anhldptit2610/dalws/hardware/dalws/dalws.kicad_sch

## KiCad design hardware/dalws/dalws.kicad_sch (2024-07-06)

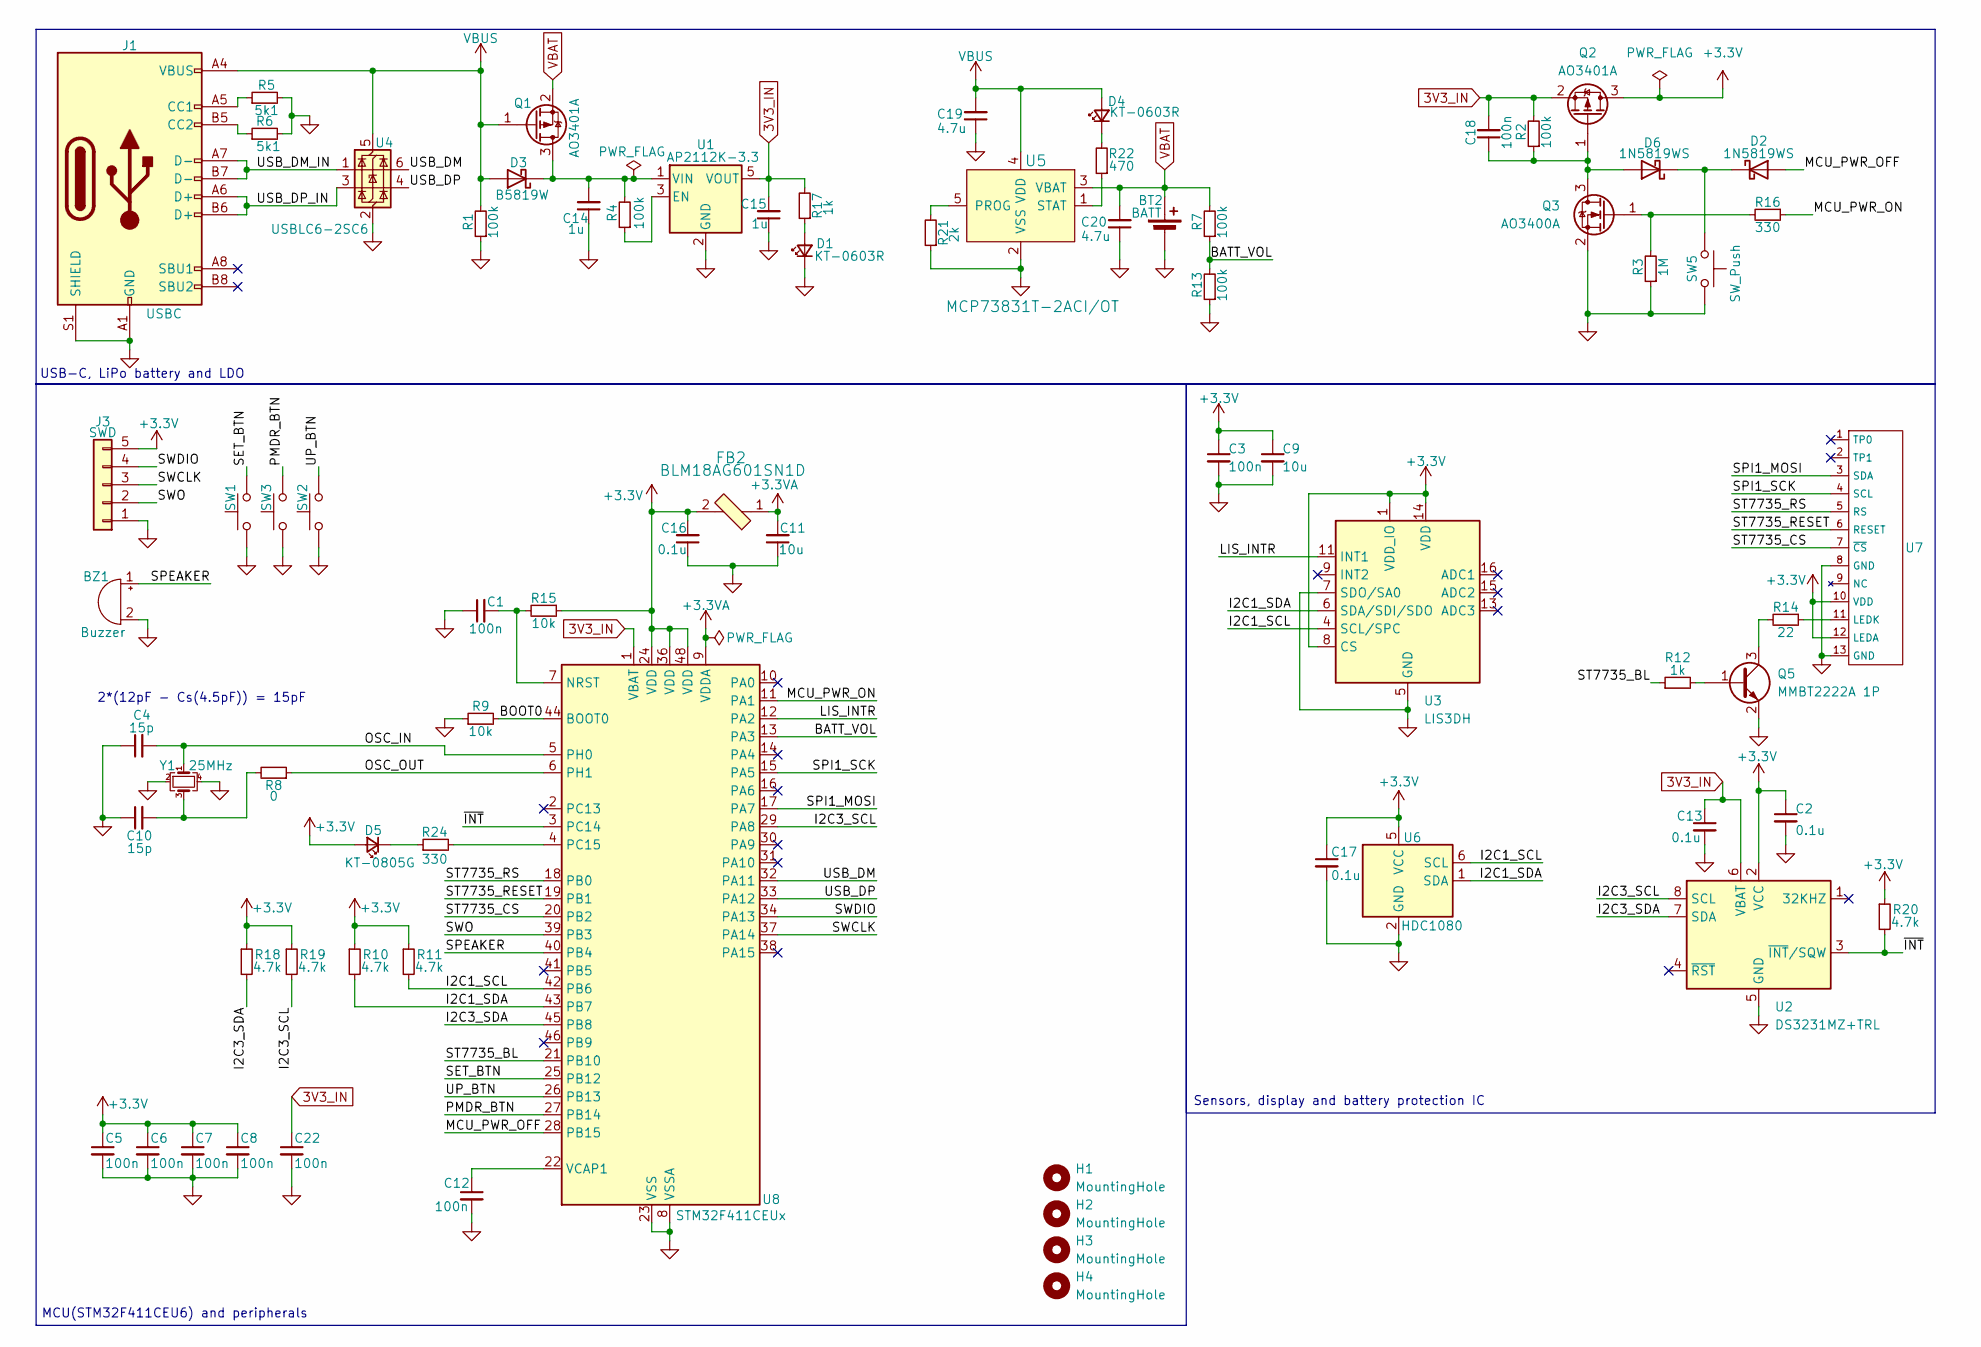
[picture p3: schematic dalws.kicad_sch]

Parts:
BT2: BATT; PinHeader_1x02_P2.54mm_Vertical
BZ1: Buzzer; TMB09A05
C1, C3, C5, C6, C7, C8, C12, C18, C22: 100n; C_0402_1005Metric_Pad0.74x0.62mm_HandSolder
C2, C13, C16, C17: 0.1u; C_0402_1005Metric_Pad0.74x0.62mm_HandSolder
C4, C10: 15p; C_0402_1005Metric_Pad0.74x0.62mm_HandSolder
C9, C11: 10u; C_0402_1005Metric_Pad0.74x0.62mm_HandSolder
C14, C15: 1u; C_0402_1005Metric_Pad0.74x0.62mm_HandSolder
C19, C20: 4.7u; C_0805_2012Metric
D1, D4: KT-0603R; LED_0603_1608Metric_Pad1.05x0.95mm_HandSolder
D2, D6: 1N5819WS; D_SOD-323
D3: B5819W
D5: KT-0805G; LED_0603_1608Metric_Pad1.05x0.95mm_HandSolder
FB2: BLM18AG601SN1D; 0603; MPN BLM18AG601SN1D; Digi-Key_PN 490-1014-1-ND
H1, H2, H3, H4: MountingHole; MountingHole_2.7mm_M2.5_DIN965
J1: USBC; USB_C_Receptacle_G-Switch_GT-USB-7010ASV
J3: SWD; PinHeader_1x05_P2.54mm_Vertical
Q1, Q2: AO3401A; SOT-23
Q3: AO3400A; SOT-23
Q5: MMBT2222A 1P; SOT-23
R1, R2, R4, R7, R13: 100k; R_0402_1005Metric_Pad0.72x0.64mm_HandSolder
R3: 1M; R_0402_1005Metric_Pad0.72x0.64mm_HandSolder
R5, R6: 5k1; R_0402_1005Metric_Pad0.72x0.64mm_HandSolder
R8: 0; R_0402_1005Metric_Pad0.72x0.64mm_HandSolder
R9, R15: 10k; R_0402_1005Metric_Pad0.72x0.64mm_HandSolder
R10, R11, R18, R19, R20: 4.7k; R_0805_2012Metric
R12, R17: 1k; R_0402_1005Metric_Pad0.72x0.64mm_HandSolder
R14: 22; R_0402_1005Metric_Pad0.72x0.64mm_HandSolder
R16: 330; R_0402_1005Metric_Pad0.72x0.64mm_HandSolder
R21: 2k; R_0402_1005Metric_Pad0.72x0.64mm_HandSolder
R22: 470; R_0402_1005Metric_Pad0.72x0.64mm_HandSolder
R24: 330; R_0805_2012Metric
SW1, SW2, SW3, SW5: SW_Push; GT-TC060A-H025-L1
U1: AP2112K-3.3; SOT-23-5
U2: DS3231MZ+TRL; SOIC-8_3.9x4.9mm_P1.27mm
U3: LIS3DH; LIS3DHTR
U4: USBLC6-2SC6; SOT-23-6
U5: MCP73831T-2ACI/OT; SOT-753; MPN MCP73831T-2ACI/OT; Digi-Key_PN MCP73831T-2ACI/OTCT-ND
U6: HDC1080; Texas_PWSON-N6
U7: OLED-SMD_ST7735S
U8: STM32F411CEUx; QFN-48-1EP_7x7mm_P0.5mm_EP5.6x5.6mm
Y1: 25MHz; Crystal_SMD_3225-4Pin_3.2x2.5mm

Connections:
3V3_IN: C13.1, C15.2, C18.2, C22.1, Q2.2 (S), R2.2, R17.2, U1.5 (VOUT), U2.6 (VBAT), U8.1 (VBAT)
+3.3V: C2.1, C3.1, C5.1, C6.1, C7.1, C8.1, C9.1, C16.2, C17.1, D5.2 (A), FB2.2, J3.5, Q2.3 (D), R10.1, R11.1, R15.1, R18.1, R19.1, R20.1, U2.2 (VCC), U3.1 (VDD_IO), U3.8 (CS), U3.14 (VDD), U6.5 (VCC), U7.10 (VDD), U7.12 (LEDA), U8.24 (VDD), U8.36 (VDD), U8.48 (VDD)
+3.3VA: C11.2, FB2.1, U8.9 (VDDA)
BATT_VOL: R7.1, R13.2, U8.13 (PA3)
BOOT0: R9.2, U8.44 (BOOT0)
GND: BT2.2 (-), BZ1.2 (-), C1.1, C2.2, C3.2, C4.1, C5.2, C6.2, C7.2, C8.2, C9.2, C10.1, C11.1, C12.2, C13.2, C14.1, C15.1, C16.1, C17.2, C19.1, C20.1, C22.2, D1.1 (K), J1.A1 (GND), J1.A12 (GND), J1.B1 (GND), J1.B12 (GND), J1.S1 (SHIELD), J3.1, Q3.2 (S), Q5.2 (E), R1.1, R3.1, R5.2, R6.2, R9.1, R13.1, R21.1, SW1.1, SW2.1, SW3.1, SW5.1, U1.2 (GND), U2.5 (GND), U3.5 (GND), U3.7 (SDO/SA0), U3.10 (GND), U3.12 (GND), U4.2 (GND), U5.2 (VSS), U6.2 (GND), U7.8 (GND), U7.13 (GND), U8.8 (VSSA), U8.23 (VSS), U8.35 (VSS), U8.47 (VSS), U8.49 (VSS), Y1.2, Y1.4
I2C1_SCL: R11.2, U3.4 (SCL/SPC), U6.6 (SCL), U8.42 (PB6)
I2C1_SDA: R10.2, U3.6 (SDA/SDI/SDO), U6.1 (SDA), U8.43 (PB7)
I2C3_SCL: R19.2, U2.8 (SCL), U8.29 (PA8)
I2C3_SDA: R18.2, U2.7 (SDA), U8.45 (PB8)
LIS_INTR: U3.11 (INT1), U8.12 (PA2)
MCU_PWR_OFF: D2.2 (A), U8.28 (PB15)
MCU_PWR_ON: R16.1, U8.11 (PA1)
unnamed: C1.2, R15.2, U8.7 (NRST)
unnamed: C10.2, R8.2, Y1.3
unnamed: C12.1, U8.22 (VCAP1)
unnamed: C14.2, D3.1 (K), Q1.3 (D), R4.2, U1.1 (VIN)
unnamed: C18.1, D6.2 (A), Q2.1 (G), Q3.3 (D), R2.1
unnamed: D1.2 (A), R17.1
unnamed: D2.1 (K), D6.1 (K), SW5.2
unnamed: D4.1 (K), R22.2
unnamed: D5.1 (K), R24.1
unnamed: J1.A5 (CC1), R5.1
unnamed: J1.B5 (CC2), R6.1
unnamed: Q3.1 (G), R3.2, R16.2
unnamed: Q5.1 (B), R12.2
unnamed: Q5.3 (C), R14.2
unnamed: R4.1, U1.3 (EN)
unnamed: R14.1, U7.11 (LEDK)
unnamed: R21.2, U5.5 (PROG)
unnamed: R22.1, U5.1 (STAT)
unnamed: R24.2, U8.4 (PC15)
OSC_IN: C4.2, U8.5 (PH0), Y1.1
OSC_OUT: R8.1, U8.6 (PH1)
PMDR_BTN: SW3.2, U8.27 (PB14)
SET_BTN: SW1.2, U8.25 (PB12)
SPEAKER: BZ1.1 (+), U8.40 (PB4)
SPI1_MOSI: U7.3 (SDA), U8.17 (PA7)
SPI1_SCK: U7.4 (SCL), U8.15 (PA5)
ST7735_BL: R12.1, U8.21 (PB10)
ST7735_CS: U7.7 (~CS), U8.20 (PB2)
ST7735_RESET: U7.6 (RESET), U8.19 (PB1)
ST7735_RS: U7.5 (RS), U8.18 (PB0)
SWCLK: J3.3, U8.37 (PA14)
SWDIO: J3.4, U8.34 (PA13)
SWO: J3.2, U8.39 (PB3)
UP_BTN: SW2.2, U8.26 (PB13)
USB_DM: U4.6 (I/O1), U8.32 (PA11)
USB_DM_IN: J1.A7 (D-), J1.B7 (D-), U4.1 (I/O1)
USB_DP: U4.4 (I/O2), U8.33 (PA12)
USB_DP_IN: J1.A6 (D+), J1.B6 (D+), U4.3 (I/O2)
VBAT: BT2.1 (+), C20.2, Q1.2 (S), R7.2, U5.3 (VBAT)
VBUS: C19.2, D3.2 (A), D4.2 (A), J1.A4 (VBUS), J1.A9 (VBUS), J1.B4 (VBUS), J1.B9 (VBUS), Q1.1 (G), R1.2, U4.5 (VBUS), U5.4 (VDD)
~INT: R20.2, U2.3 (~INT/SQW), U8.3 (PC14)

Notes on the sheet:
MCU(STM32F411CEU6) and peripherals
2*(12pF - Cs(4.5pF)) = 15pF
USB-C, LiPo battery and LDO
Sensors, display and battery protection IC
