anhldptit2610/dalws/firmware/dalws/Core/Src/hdc1080.c

#include "hdc1080.h"

I2C_HandleTypeDef *i2cHandler = NULL;
// uint16_t tempHump[2];

void hdc1080_send_data_request(void)
{
    uint8_t reg = HDC1080_TEMP;

    HAL_I2C_Master_Transmit(i2cHandler, HDC1080_ADDR, (uint8_t *)&reg, 1, 100);
}

void hdc1080_get_data(uint16_t *tempHump)
{
    uint8_t reg = 0x00, data[4];

    HAL_I2C_Master_Receive(i2cHandler, HDC1080_ADDR, (uint8_t *)data, 4, 100);
    tempHump[0] = TO_U16(data[1], data[0]);
    tempHump[1] = TO_U16(data[3], data[2]);
}

void hdc1080_init(I2C_HandleTypeDef *hi2c)
{
    uint8_t data[3];
    uint16_t val;
    i2cHandler = hi2c;

    HAL_Delay(15);
    data[0] = HDC1080_CONF;
    // acquisite both temp and humid, 14-bit resolution
    val = 0x00 | (1U << 13);
    data[1] = LBYTE(val);
    data[2] = RBYTE(val);
    HAL_I2C_Master_Transmit(i2cHandler, HDC1080_ADDR, data, 3, 100);
}
