anhldptit2610/dalws/firmware/dalws/Core/Inc/lv_port_indev.h

/**
 * @file lv_port_indev_templ.h
 *
 */

/*Copy this file as "lv_port_indev.h" and set this value to "1" to enable content*/
#if 1

#ifndef LV_PORT_INDEV_TEMPL_H
#define LV_PORT_INDEV_TEMPL_H

#ifdef __cplusplus
extern "C" {
#endif

/*********************
 *      INCLUDES
 *********************/
#if defined(LV_LVGL_H_INCLUDE_SIMPLE)
#include "lvgl.h"
#else
#include "lvgl.h"
#endif

/*********************
 *      DEFINES
 *********************/

/**********************
 *      TYPEDEFS
 **********************/

/**********************
 * GLOBAL PROTOTYPES
 **********************/
extern lv_group_t *set_group;

void lv_port_indev_init(void);

/**********************
 *      MACROS
 **********************/

#ifdef __cplusplus
} /*extern "C"*/
#endif

#endif /*LV_PORT_INDEV_TEMPL_H*/

#endif /*Disable/Enable content*/
